rodrigokimura/roki/roki/firmware/config.py

from __future__ import annotations

import json

from roki.firmware import logging
from roki.firmware.keys import BaseKey, init
from roki.firmware.params import Params

logger = logging.getLogger(__name__)


def parse_color(
    color: str | list[int | str] | tuple[int | str, int | str, int | str],
) -> tuple[int, int, int]:
    if isinstance(color, str):
        if color[0] == "#":
            color = color[1:]
        if len(color) != 6:
            raise ValueError("Invalid color")
        r = color[:2]
        g = color[2:4]
        b = color[4:]
        return int(r, 16), int(g, 16), int(b, 16)

    if isinstance(color, (list, tuple)):
        return int(color[0]), int(color[1]), int(color[2])

    raise NotImplementedError


class Layer:
    name: str
    color: tuple[int, int, int]
    primary_keys: tuple[BaseKey, ...]
    secondary_keys: tuple[BaseKey, ...]
    primary_encoder_cw: BaseKey
    primary_encoder_ccw: BaseKey
    secondary_encoder_cw: BaseKey
    secondary_encoder_ccw: BaseKey

    @classmethod
    def from_dict(cls, data: dict) -> Layer:
        is_left_side = Params().IS_LEFT_SIDE
        i = cls()
        i.name = data.get("name", "no name")
        c = data.get("color", "#000000")
        i.color = parse_color(c)

        i.primary_keys = tuple(
            BaseKey.build(k)
            for row in data.get(
                "primary_keys" if is_left_side else "secondary_keys",
                (("",),),
            )
            for k in (reversed(row) if is_left_side else row)
        )

        cw, ccw = data.get("primary_encoder", ("", ""))
        i.primary_encoder_cw = BaseKey.build(cw)
        i.primary_encoder_ccw = BaseKey.build(ccw)

        i.secondary_keys = tuple(
            BaseKey.build(k)
            for row in data.get(
                "secondary_keys" if is_left_side else "primary_keys",
                (("",),),
            )
            for k in (row if is_left_side else reversed(row))
        )

        cw, ccw = data.get("primary_encoder", ("", ""))
        i.secondary_encoder_cw = BaseKey.build(cw)
        i.secondary_encoder_ccw = BaseKey.build(ccw)
        return i


class Config:
    __slots__ = (
        "layers",
        "is_left_side",
        "layer_index",
        "extras",
    )

    layers: tuple[Layer, ...]
    is_left_side: bool
    layer_index: int
    extras: bool

    def __init__(self, layers: list[dict] | None = None) -> None:
        init(self)
        self.layer_index = 0
        self.extras = False
        self.layers = tuple(Layer.from_dict(layer) for layer in layers or tuple())

        is_left_side = Params().IS_LEFT_SIDE
        logger.debug(f"Left side: {is_left_side}")
        self.is_left_side = is_left_side

    @property
    def layer(self) -> Layer:
        return self.layers[self.layer_index]

    @classmethod
    def read(cls) -> Config:
        global _config
        if _config is None:
            with open("config.json") as file:
                config: dict = json.load(file)
            _config = cls(
                layers=config.get("layers", []),
            )
        return _config


_config: Config | None = None
