rodrigokimura/roki/roki/firmware/service.py

import _bleio
from adafruit_ble.attributes import Attribute
from adafruit_ble.characteristics import Characteristic, ComplexCharacteristic
from adafruit_ble.services import Service
from adafruit_ble.uuid import VendorUUID

BUFFER_SIZE = 4


class PacketBufferUUID(VendorUUID):
    def __init__(self, uuid16):
        uuid128 = bytearray("reffuBtekcaP".encode("utf-8") + b"\x00\x00\xaf\xad")
        uuid128[-3] = uuid16 >> 8
        uuid128[-4] = uuid16 & 0xFF
        super().__init__(uuid128)


class PacketBufferCharacteristic(ComplexCharacteristic):
    def __init__(
        self,
        *,
        uuid=None,
        buffer_size=4,
        properties=Characteristic.WRITE_NO_RESPONSE
        | Characteristic.NOTIFY
        | Characteristic.READ,
        read_perm=Attribute.OPEN,
        write_perm=Attribute.OPEN,
    ):
        self.buffer_size = buffer_size
        super().__init__(
            uuid=uuid,
            properties=properties,
            read_perm=read_perm,
            write_perm=write_perm,
            max_length=BUFFER_SIZE,
            fixed_length=False,
        )

    def bind(self, service: Service):
        bound_characteristic = super().bind(service)
        return _bleio.PacketBuffer(
            bound_characteristic,
            buffer_size=self.buffer_size,
            max_packet_size=BUFFER_SIZE,
        )


class RokiService(Service):
    uuid = PacketBufferUUID(0x0001)

    packets = PacketBufferCharacteristic(uuid=PacketBufferUUID(0x0101))

    def readinto(self, buf: bytearray) -> tuple[int, int, int, int]:
        if self.packets.readinto(buf):  # type: ignore
            return buf[0], buf[1], buf[2], buf[3]
        return (0, 0, 0, 0)

    def write(self, buf: bytes, *, header: bytes | None = None) -> int:
        return self.packets.write(buf, header=header)  # type: ignore
