rodrigokimura/roki/roki/cli/html_generator.py

import json

import minify_html
from jinja2 import Environment, PackageLoader

from roki.cli.config.keys import KEYS


class Generator:
    def __init__(self, minify=True) -> None:
        self.minify = minify
        self.env = Environment(
            loader=PackageLoader("roki"),
            autoescape=False,
        )

    def get_html(self):
        keys = json.dumps([k.model_dump() for k in KEYS], separators=(",", ":"))
        template = self.env.get_template("base.html")
        html = template.render(keys=keys)

        if self.minify:
            html = minify_html.minify(
                html,
                minify_js=True,
                minify_css=True,
            )

        return html

    def generate_html(self):
        html = self.get_html()
        with open("index.html", mode="w+") as f:
            f.write(html)
