rodrigokimura/roki/roki/firmware/calibration.py

import json
import time

from adafruit_ticks import ticks_ms
from analogio import AnalogIn
from digitalio import DigitalInOut

from roki.firmware import logging
from roki.firmware.buzzer import Buzzer
from roki.firmware.utils import Loop, blink_led

logger = logging.getLogger(__name__)


class BaseCalibration:
    def __init__(
        self,
        button: DigitalInOut,
        thumb_stick_x: AnalogIn,
        thumb_stick_y: AnalogIn,
        buzzer: Buzzer,
        release_time: float = 5.0,
        mid_time: float = 5.0,
        max_iterations: int = 0,
    ):
        self.button = button
        self.thumb_stick_x = thumb_stick_x
        self.thumb_stick_y = thumb_stick_y
        self.buzzer = buzzer
        self.max_x = -float("inf")
        self.min_x = float("inf")
        self.mid_x = 0.0
        self.lower_mid_x = 0.0
        self.upper_mid_x = 0.0
        self.lower_mid_y = 0.0
        self.upper_mid_y = 0.0
        self.max_y = -float("inf")
        self.mid_y = 0.0
        self.min_y = float("inf")
        self.release_time = release_time
        self.mid_time = mid_time

        self.running = True
        self._read = False
        self._limit = 0.05
        self.max_iterations = max_iterations

    def start(self) -> None:
        logger.info("Starting calibration...")

        if not self._startup_condition():
            self.button.deinit()
            return

        self._notify_start()

        # allow user to release the button
        time.sleep(self.release_time)

        self._get_mid_values()
        self._notify_rotation()

        for _ in Loop(self.max_iterations, lambda: not self.running).iterate():
            self.max_x = max(self.max_x, self.thumb_stick_x.value)
            self.min_x = min(self.min_x, self.thumb_stick_x.value)

            self.max_y = max(self.max_y, self.thumb_stick_y.value)
            self.min_y = min(self.min_y, self.thumb_stick_y.value)

            self._check_for_stop_criteria()

        self._write_config()
        self._notify_end()
        self.button.deinit()

    def _startup_condition(self) -> bool:
        raise NotImplementedError

    def _get_mid_values(self) -> None:
        raise NotImplementedError

    def _notify_start(self) -> None:
        raise NotImplementedError

    def _notify_rotation(self) -> None:
        raise NotImplementedError

    def _notify_end(self) -> None:
        raise NotImplementedError

    def _check_for_stop_criteria(self) -> None:
        raise NotImplementedError

    def _write_config(self) -> None:
        raise NotImplementedError

    def read(self) -> None:
        raise NotImplementedError

    def get_normalized(self, x: int, y: int) -> tuple[float, float]:
        if self._read is False:
            self.read()

        return self._get_normalized_x(x), self._get_normalized_y(y)

    def _get_normalized_x(self, x: int) -> float:
        if x < self.lower_mid_x:
            return -max(
                min((self.lower_mid_x - x) / (self.lower_mid_x - self.min_x), 1.0), 0.0
            )
        if x > self.upper_mid_x:
            return max(
                min((x - self.upper_mid_x) / (self.max_x - self.upper_mid_x), 1.0), 0.0
            )
        return 0.0

    def _get_normalized_y(self, y: int) -> float:
        if y < self.lower_mid_y:
            return -max(
                min((self.lower_mid_y - y) / (self.lower_mid_y - self.min_y), 1.0), 0.0
            )
        if y > self.upper_mid_y:
            return max(
                min((y - self.upper_mid_y) / (self.max_y - self.upper_mid_y), 1.0), 0.0
            )
        return 0.0


class Calibration(BaseCalibration):
    def _startup_condition(self) -> bool:
        return not self.button.value

    def _notify_start(self) -> None:
        blink_led()
        self.buzzer.play_notes(
            (
                ("C4", 1),
                ("D4", 1),
            ),
            0.5,
        )

    def _notify_rotation(self) -> None:
        blink_led()
        self.buzzer.play_by_note("C4", 0.5)

    def _notify_end(self) -> None:
        blink_led()
        self.buzzer.play_by_note("C4", 0.5)

    def _get_mid_values(self):
        start = ticks_ms()
        current = 0

        while current < start + self.mid_time * 1000:
            self.mid_x = self.thumb_stick_x.value
            self.mid_y = self.thumb_stick_y.value
            current = ticks_ms()

    def _check_for_stop_criteria(self) -> None:
        if self._startup_condition():
            self.running = False

    def _write_config(self) -> None:
        data = {
            "min_x": self.min_x,
            "mid_x": self.mid_x,
            "max_x": self.max_x,
            "min_y": self.min_y,
            "mid_y": self.mid_y,
            "max_y": self.max_y,
        }

        try:
            with open("calibration.json", mode="w") as file:
                json.dump(data, file)
        except OSError:
            pass

    def read(self) -> None:
        with open("calibration.json", mode="r") as file:
            data = json.load(file)

        self.min_x = float(data["min_x"])
        self.mid_x = float(data["mid_x"])
        self.max_x = float(data["max_x"])
        self.min_y = float(data["min_y"])
        self.mid_y = float(data["mid_y"])
        self.max_y = float(data["max_y"])

        delta = (self.max_x - self.mid_x) * self._limit
        self.upper_mid_x = self.mid_x + delta

        delta = (self.mid_x - self.min_x) * self._limit
        self.lower_mid_x = self.mid_x - delta

        delta = (self.max_y - self.mid_y) * self._limit
        self.upper_mid_y = self.mid_y + delta

        delta = (self.mid_y - self.min_y) * self._limit
        self.lower_mid_y = self.mid_y - delta

        del self.mid_x
        del self.mid_y
